sadeus/perfilador_soma/circuito/design/analisis_amp/analisis/led_azul_rampa.png

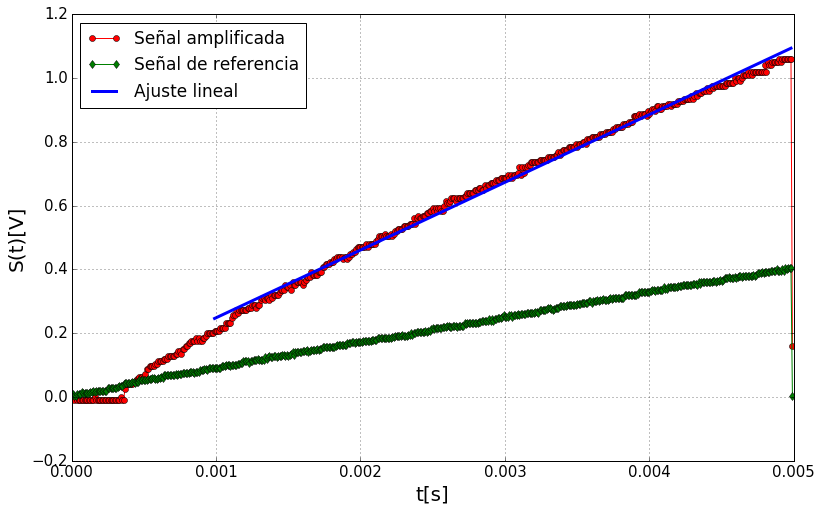
circuito/design/analisis_amp/analisis/led_azul_rampa.png
