sadeus/perfilador_soma/circuito/design/analisis_amp/analisis/led_rojo_rampa.png

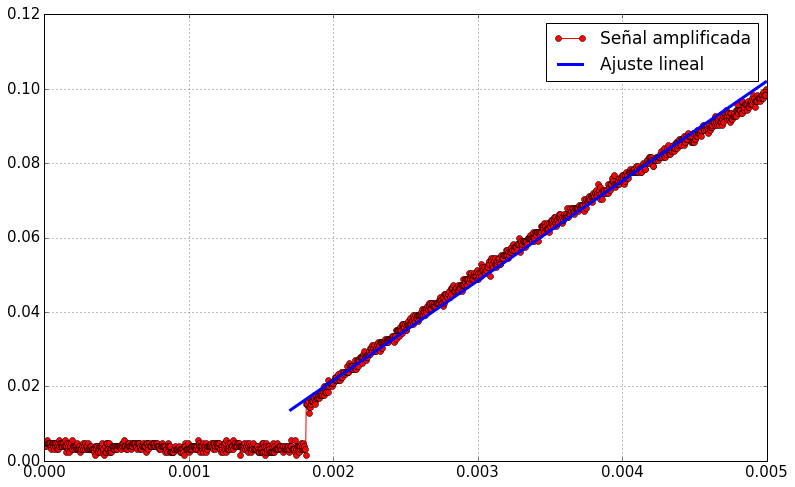
circuito/design/analisis_amp/analisis/led_rojo_rampa.png
