sadeus/perfilador_soma/perfilador/mecanica/nema8/tambor.stl

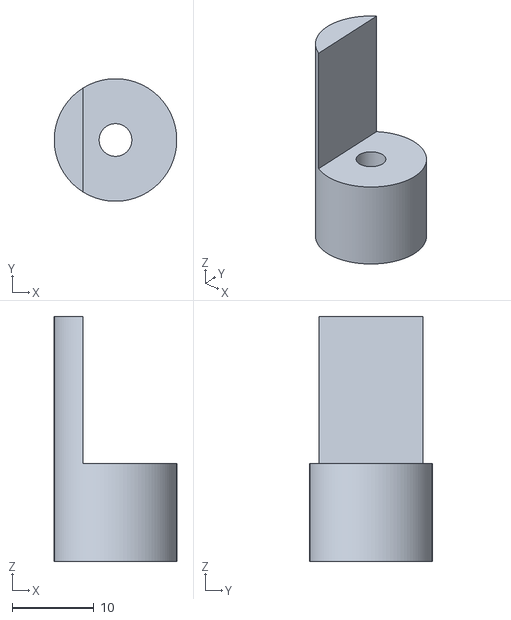
[picture p57: CAD file, 2016-06-30]
perfilador/mecanica/nema8/tambor.stl
15.0 x 15.0 x 30.0
