sadeus/perfilador_soma/polarimetro/design/soporte_polarimetro.dxf

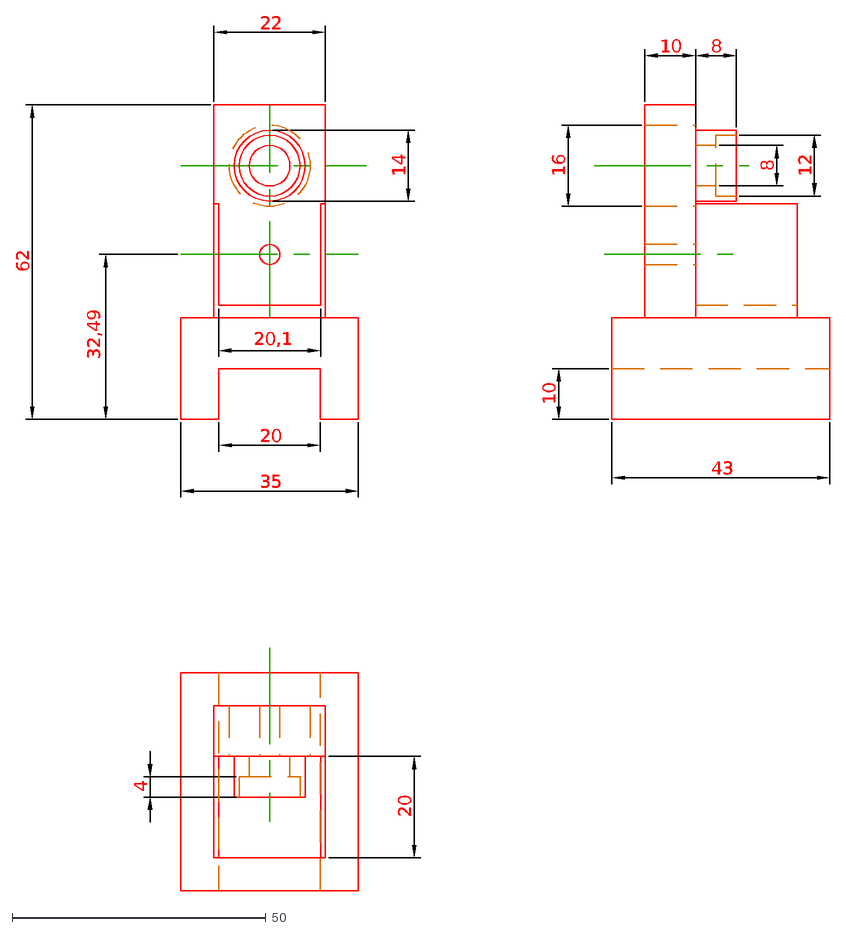
[picture p58: CAD file, 2016-07-12]
polarimetro/design/soporte_polarimetro.dxf
35
20
32,49
62
22
20,1
14
12
8
10
43
4
16
