sadeus/perfilador_soma/perfilador/mecanica/nema17/soporte/soporte.sldprt

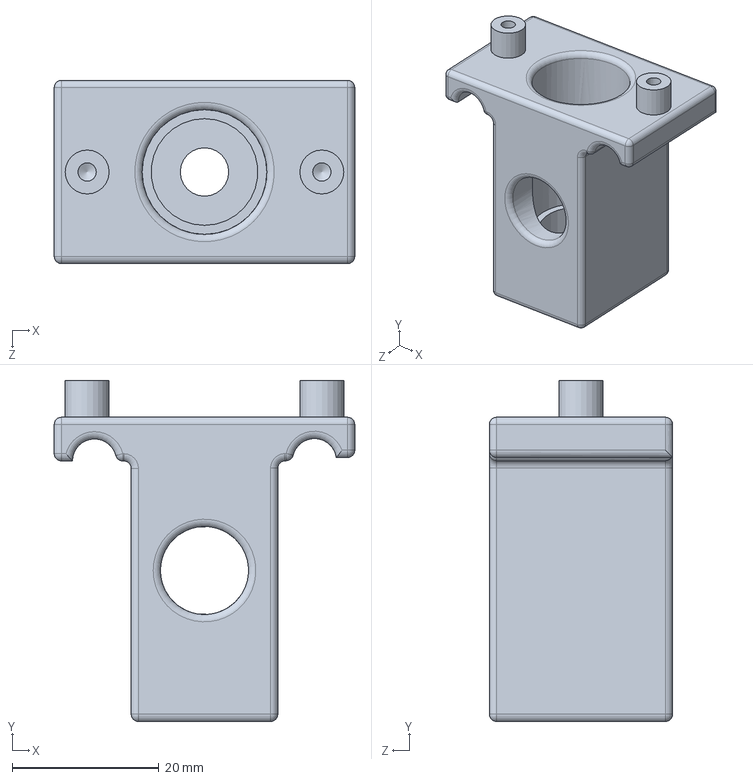
[picture p59: CAD file, 2016-06-13]
perfilador/mecanica/nema17/soporte/soporte.sldprt
41.0 x 46.5 x 25.0 mm
