sadeus/perfilador_soma/perfilador/mecanica/nema17/tambor/tambor.sldprt

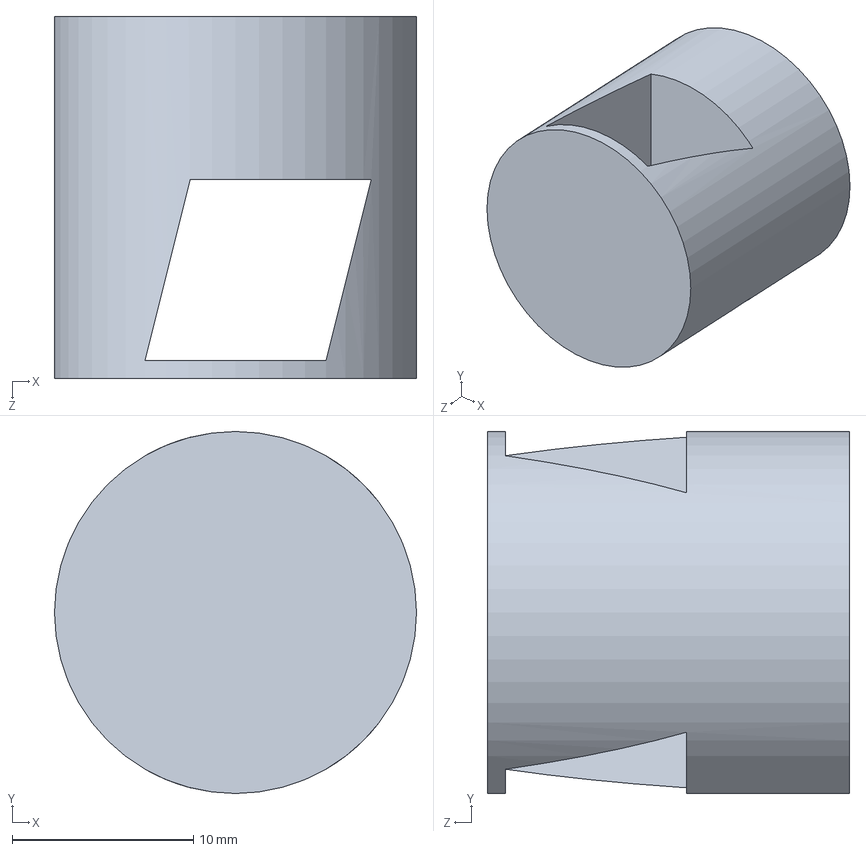
[picture p60: CAD file, 2016-06-13]
perfilador/mecanica/nema17/tambor/tambor.sldprt
20.0 x 20.0 x 20.0 mm
