sadeus/perfilador_soma/perfilador/mecanica/nema8/tambor_v4.SLDPRT

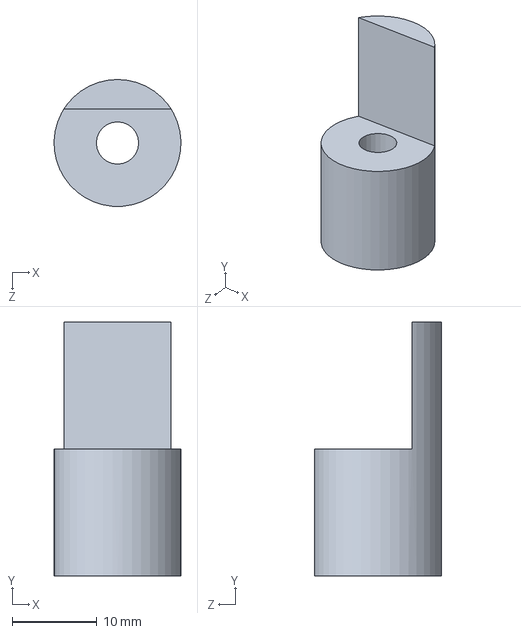
[picture p61: CAD file, 2016-06-13]
perfilador/mecanica/nema8/tambor_v4.SLDPRT
15.0 x 30.0 x 15.0 mm
