sadeus/perfilador_soma/polarimetro/design/soporte.stl

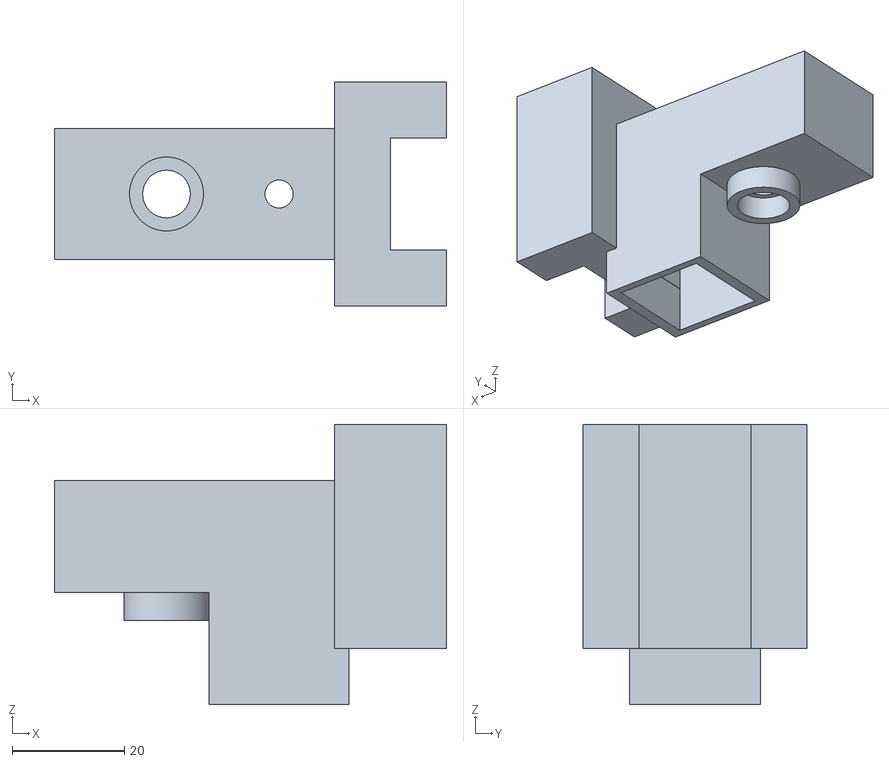
[picture p62: CAD file, 2016-06-13]
polarimetro/design/soporte.stl
70.0 x 40.0 x 50.0
