sadeus/perfilador_soma/perfilador/mecanica/nema8/soporte.SLDPRT

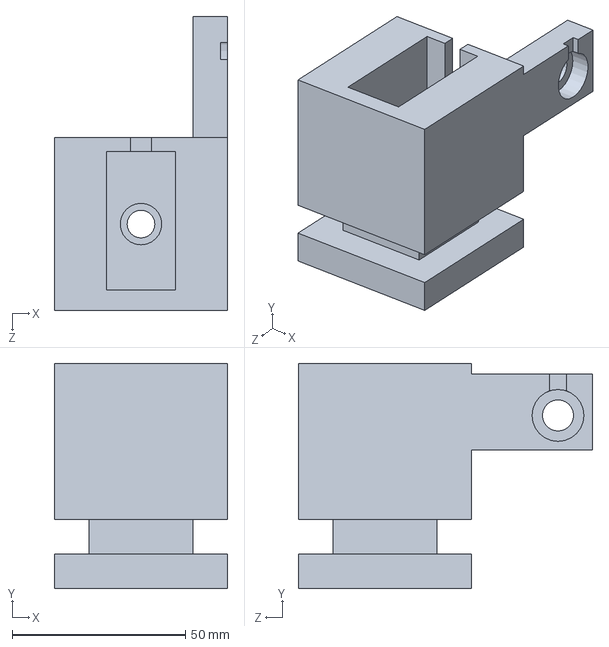
[picture p63: CAD file, 2016-06-13]
perfilador/mecanica/nema8/soporte.SLDPRT
50.0 x 65.0 x 85.0 mm
