sadeus/perfilador_soma/perfilador/mecanica/nema8/carcaza.SLDPRT

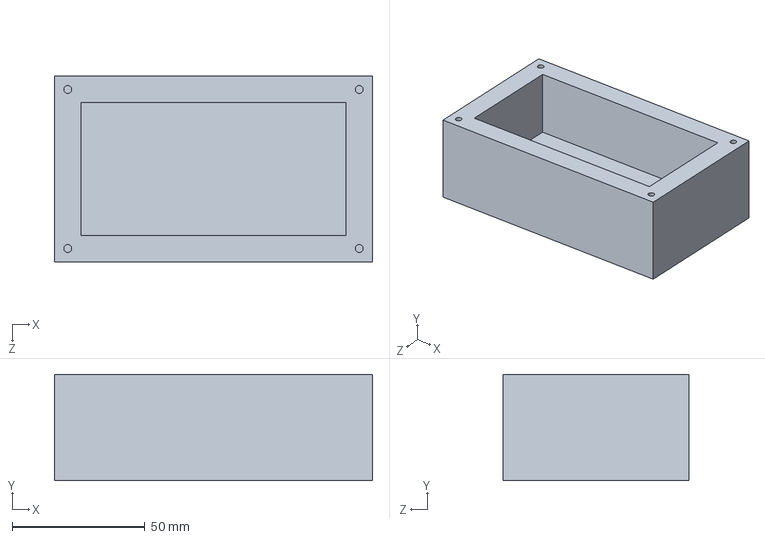
[picture p64: CAD file, 2016-06-13]
perfilador/mecanica/nema8/carcaza.SLDPRT
120.0 x 40.0 x 70.0 mm
