sadeus/perfilador_soma/perfilador/mecanica/nema17/soporte/soporte_v5_solido.sldprt

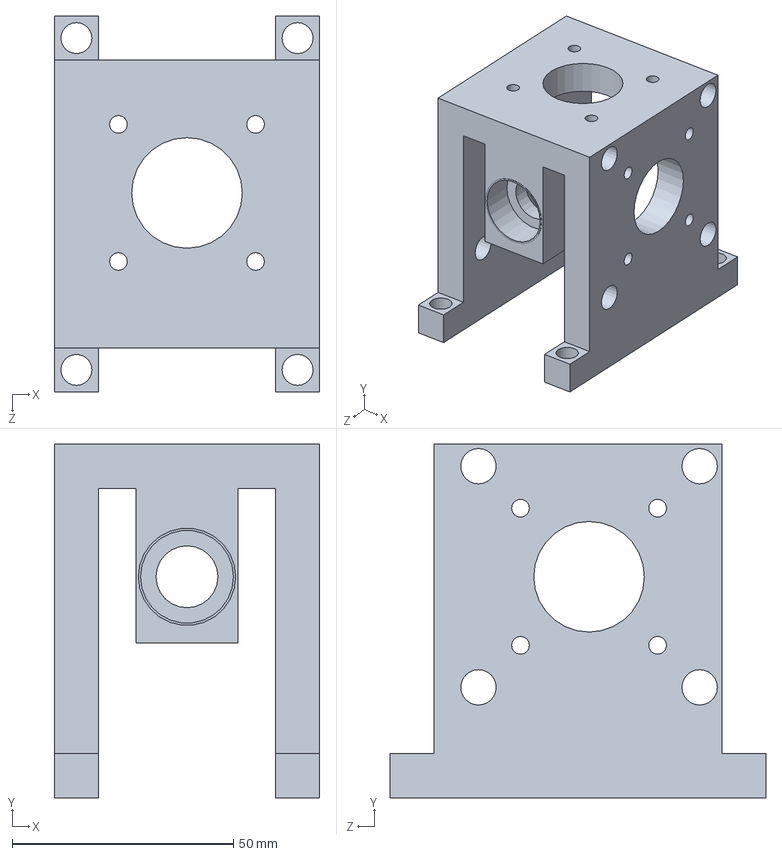
[picture p65: CAD file, 2016-06-13]
perfilador/mecanica/nema17/soporte/soporte_v5_solido.sldprt
60.0 x 80.0 x 85.0 mm
