sadeus/perfilador_soma/perfilador/mecanica/nema8/perfilador.scad

include <soporte.scad>
include <tambor.scad>

soporte();

translate([80,0,0]){
    tambor();
}
      
