sadeus/perfilador_soma/perfilador/mecanica/nema8/soporte.scad

module soporte() {
    
    sizeSoporte = [40,40,60];
    
    alturaEje = 50;
    
    //Tamaño del motor
    motorSize = [20.2,20.2, 28.2];

    alturaPerros = 10;
    anchoPerros = 15;

    distFotodiodo = 50;

    diametroPhExt = 12;
    diametroPhInt = 8;

    $fn = 100;
    
    difference(){
        translate([0,0,sizeSoporte[2] / 2]){
            
            difference(){

                cube(sizeSoporte, center=true);
              
                
                cylinder(h= alturaEje + motorSize[0], r=3.5, center=true);
                
                translate([0,0,5]){
                    cylinder(h= alturaEje + motorSize[0] - 15, r=6 , center=true);
                }
                

                //Perros
                # translate([0,0,-5]){
                    difference(){
                        cube(sizeSoporte - [0,0,1] * (sizeSoporte[2] - alturaPerros), center=true);
                        cube(sizeSoporte - anchoPerros * [1,1,0] - (sizeSoporte[2] - alturaPerros) * [0,0,1], center=true);
                    }
                }
            }
        }

        //Encastre del motor
        translate([-5, 0, alturaEje]){
            cube([motorSize[2] + 10 ,motorSize[1],motorSize[0]],center=true);   
            
    }
        
        translate([0,0,alturaEje]){
            rotate([0, 90, 0]){
                cylinder(d=6, h=motorSize[2], $fn=50);
            }
        }
        
        
    }




    //Soporte fotodiodo
     translate([distFotodiodo, (8/2 - sizeSoporte[1]/2), alturaEje]){
        difference(){
            translate([-distFotodiodo/4 , 0, 0]){
                cube([distFotodiodo/2 + 20, 8, 20], center = true);
            }

            rotate([90,0,0]){
                cylinder(d = diametroPhInt, h = 30, center = true);
                translate([0,0,6]){
                    cylinder(d = diametroPhExt, h=10, center = true);
                }
            }

            
        }
    }
}
