sadeus/perfilador_soma/perfilador/mediciones/pruebas/2015/med_4_11/data_1902.csv

0.000000000000000000e+00 8.600000000000000000e+01
1.550000000000000000e-04 8.500000000000000000e+01
3.119999999999999944e-04 8.600000000000000000e+01
4.669999999999999672e-04 8.600000000000000000e+01
6.250000000000000130e-04 8.700000000000000000e+01
7.799999999999999859e-04 8.500000000000000000e+01
9.370000000000000074e-04 8.600000000000000000e+01
1.091999999999999872e-03 8.800000000000000000e+01
1.250000000000000026e-03 8.700000000000000000e+01
1.404999999999999999e-03 8.600000000000000000e+01
1.562999999999999936e-03 8.500000000000000000e+01
1.717999999999999909e-03 8.500000000000000000e+01
1.874999999999999931e-03 8.800000000000000000e+01
2.030000000000000120e-03 8.600000000000000000e+01
2.187999999999999841e-03 8.600000000000000000e+01
2.343000000000000031e-03 8.600000000000000000e+01
2.500000000000000052e-03 8.600000000000000000e+01
2.655999999999999941e-03 8.500000000000000000e+01
2.812999999999999962e-03 8.600000000000000000e+01
2.967999999999999718e-03 8.500000000000000000e+01
3.125999999999999873e-03 8.700000000000000000e+01
3.281000000000000062e-03 8.600000000000000000e+01
3.437999999999999650e-03 8.600000000000000000e+01
3.592999999999999840e-03 8.500000000000000000e+01
3.750999999999999994e-03 8.600000000000000000e+01
3.905999999999999750e-03 8.500000000000000000e+01
4.062999999999999771e-03 8.600000000000000000e+01
4.218999999999999660e-03 8.500000000000000000e+01
4.375999999999999682e-03 8.600000000000000000e+01
4.530999999999999438e-03 8.600000000000000000e+01
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
8.111899999999999666e-02 1.000000000000000000e+00
8.127700000000000202e-02 4.000000000000000000e+00
8.143199999999999050e-02 1.000000000000000000e+00
8.158899999999999486e-02 6.000000000000000000e+00
8.174399999999999722e-02 2.000000000000000000e+00
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
