sadeus/perfilador_soma/perfilador/mediciones/pruebas/2015/med_4_11/data_1752.png

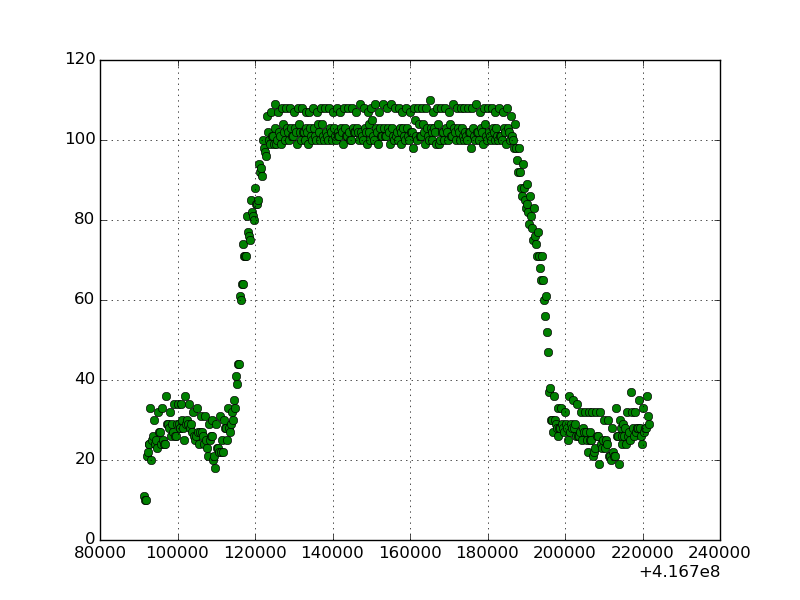
perfilador/mediciones/pruebas/2015/med_4_11/data_1752.png
