sadeus/perfilador_soma/perfilador/mediciones/pruebas/2015/med_4_11/data_1752_in.png

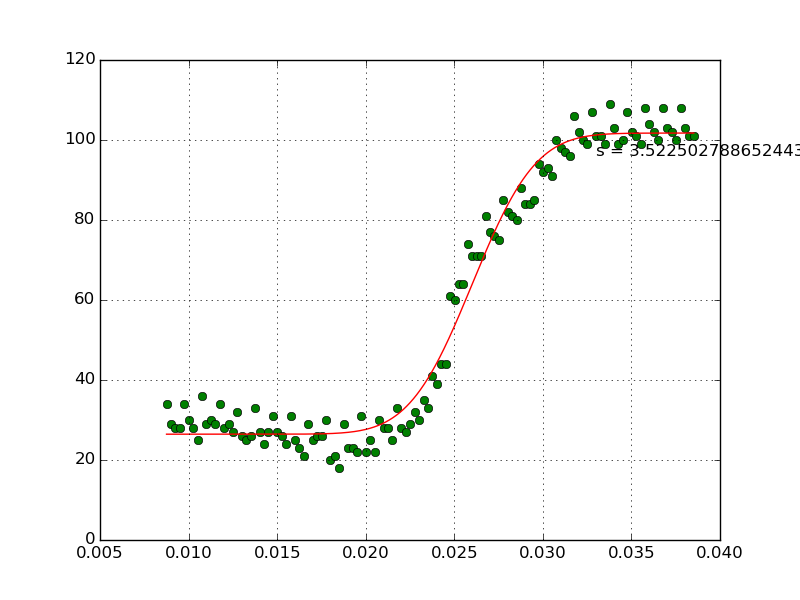
perfilador/mediciones/pruebas/2015/med_4_11/data_1752_in.png
