sadeus/perfilador_soma/perfilador/mediciones/pruebas/2015/med_13_10/data_13_10_15_sp_180_1subida.png

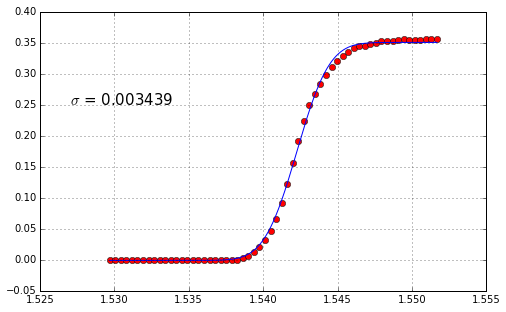
perfilador/mediciones/pruebas/2015/med_13_10/data_13_10_15_sp_180_1subida.png
