sadeus/perfilador_soma/perfilador/mediciones/pruebas/2015/med_20_10/data_19_46.png

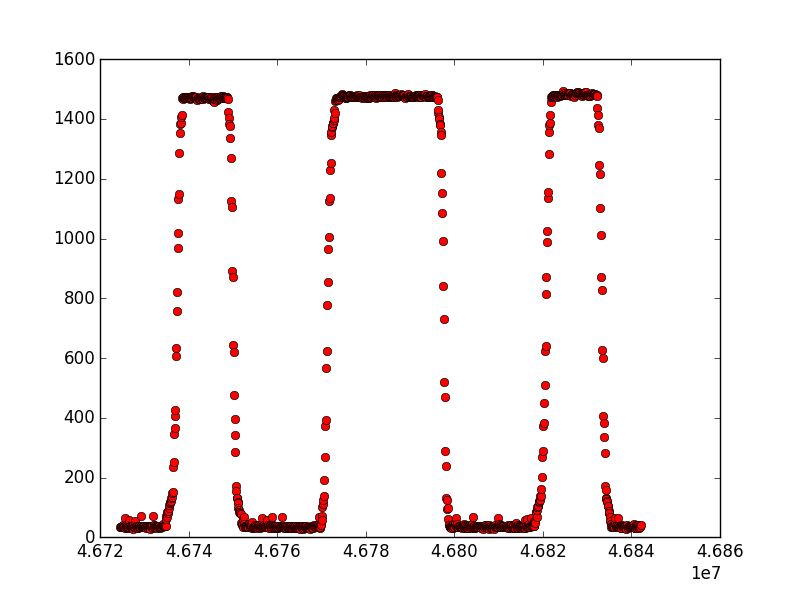
perfilador/mediciones/pruebas/2015/med_20_10/data_19_46.png
