sadeus/perfilador_soma/perfilador/mediciones/pruebas/2015/med_27_10/data_14_32.png

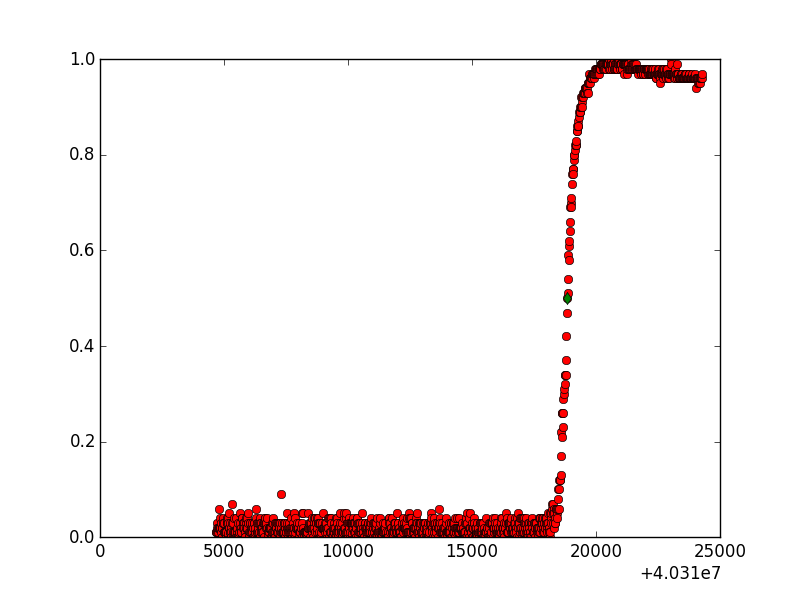
perfilador/mediciones/pruebas/2015/med_27_10/data_14_32.png
