sadeus/perfilador_soma/perfilador/mediciones/pruebas/2015/med_29_09/data_Vm1.png

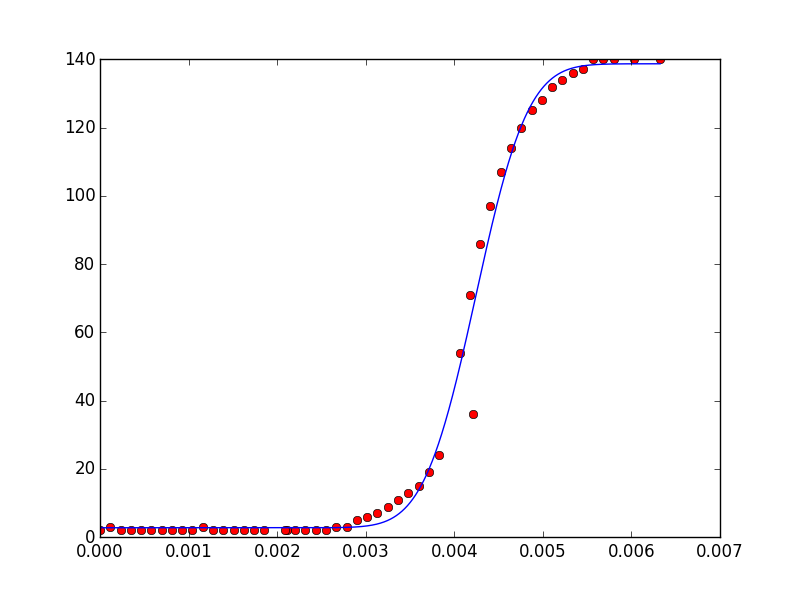
perfilador/mediciones/pruebas/2015/med_29_09/data_Vm1.png
